PA3AEF/HP8562A-Tracking-Generator/images/s11-3cm-pole-filter.jpg

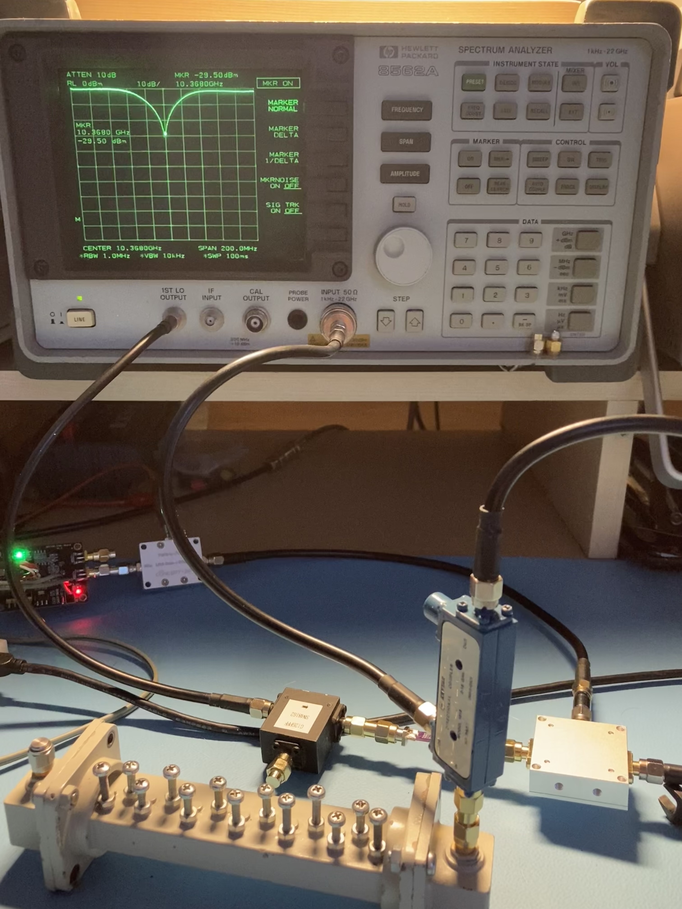
images/s11-3cm-pole-filter.jpg
